Kitsune-Robotics/KIT-Controller/Firmware/foxtool.py

#!/usr/bin/python

# Saw a lot of people using small python scripts to
# help automate the process of getting the uf2 on the rp2040

# This dosn't use scons or anything, its really just a bunch of shortcuts
# so you can quickly debug and fire up

import argparse
import subprocess
import os
import sys
from pathlib import Path


def build():
    """
    Function to handle building using CMake.
    """
    print("Building with CMake...")

    build_dir = Path("build")
    if not build_dir.exists():
        build_dir.mkdir()

    try:
        # Run CMake commands
        subprocess.run(["cmake", ".."], cwd=build_dir, check=True)
        subprocess.run(["make"], cwd=build_dir, check=True)
        print("Build completed successfully.")
    except subprocess.CalledProcessError as e:
        print(f"Build failed: {e}")
        sys.exit(1)


def flash():
    """
    Function to handle flashing the UF2 file onto the RP2040.
    """

    uf2_file = "build/src/kit-controller.uf2"

    try:
        print(f"Copying {uf2_file}")
        subprocess.run(["picotool", "load", "-f", uf2_file], check=True)

        print("Rebooting...")
        subprocess.run(["picotool", "reboot"], check=True)
    except Exception as e:
        print(f"Error flashing UF2: {e}")


def main():
    parser = argparse.ArgumentParser(description="RP2040 Development Tools")
    parser.add_argument(
        "option",
        choices=["build", "flash", "all"],
        help="Choose an operation: build, flash, or all",
    )
    args = parser.parse_args()

    if args.option == "build":
        build()
    elif args.option == "flash":
        flash()
    elif args.option == "all":
        build()
        flash()
    else:
        print(f"Unknown option: {args.option}")
        sys.exit(1)


if __name__ == "__main__":
    main()
